paddugns/rower_qube_20251-a0/RQF 20251/Soft copy/B Mask.PNG

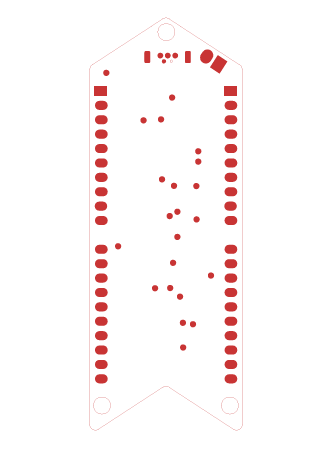
RQF 20251/Soft copy/B Mask.PNG
