paddugns/rower_qube_20251-a0/RQF 20251/Soft copy/connectors.PNG

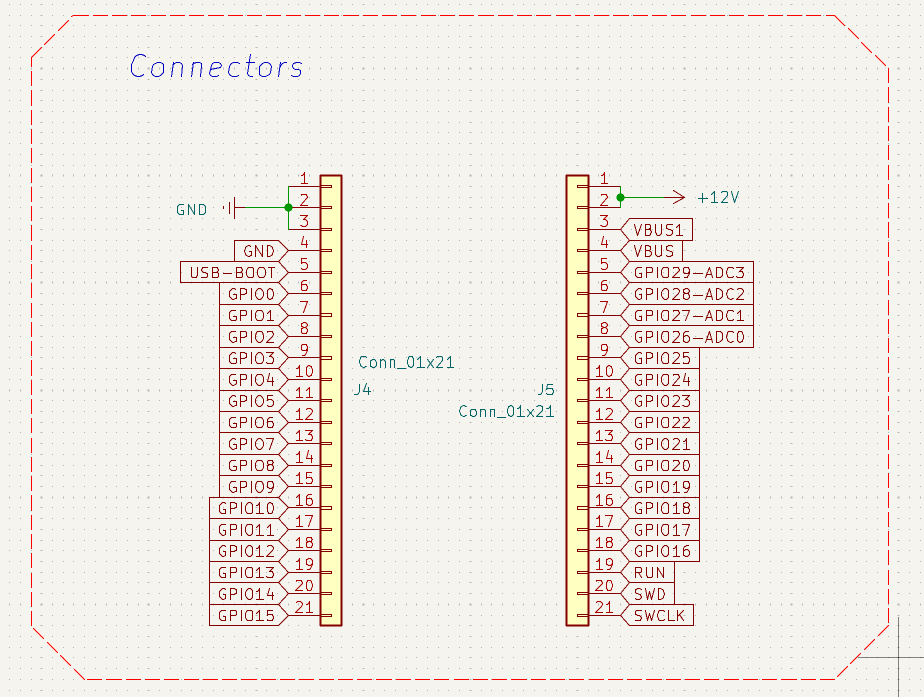
RQF 20251/Soft copy/connectors.PNG
