paddugns/rower_qube_20251-a0/RQF 20251/Soft copy/p-photo/f.JPG

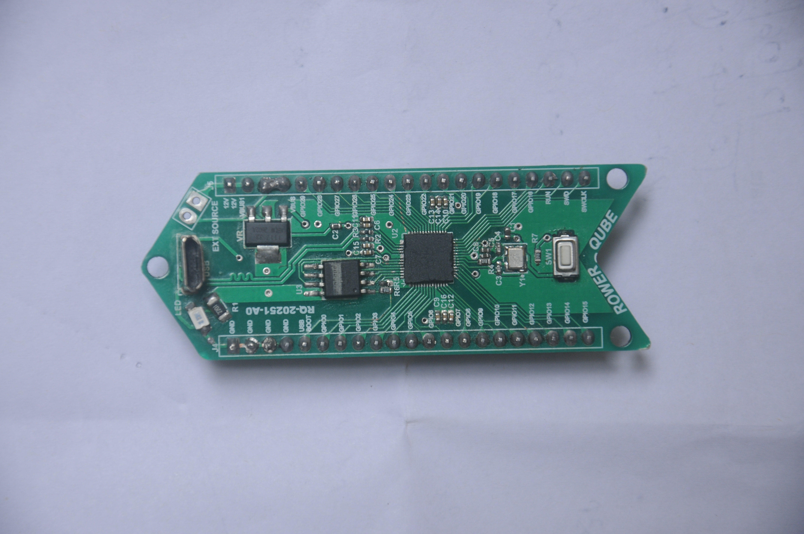
RQF 20251/Soft copy/p-photo/f.JPG
