paddugns/rower_qube_20251-a0/RQF 20251/Soft copy/PTH Drills.PNG

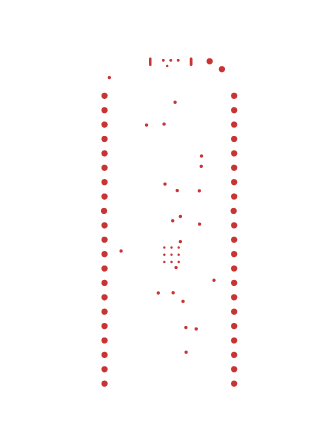
RQF 20251/Soft copy/PTH Drills.PNG
